RBersier/TPI_Horloge-Led-Capteurs/Image/Documentation/CDC/29156.jpg

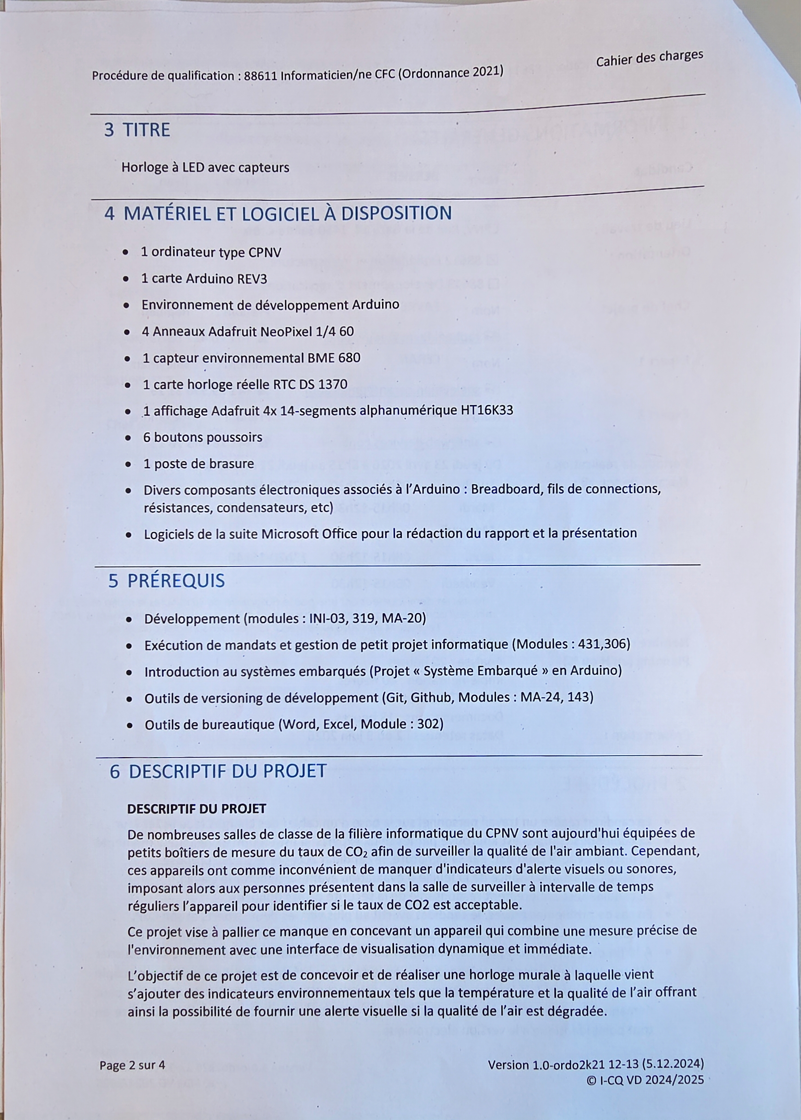
Image/Documentation/CDC/29156.jpg
