RBersier/TPI_Horloge-Led-Capteurs/Documentation/Video/Base/Red_circle_frame_transparent.svg.png

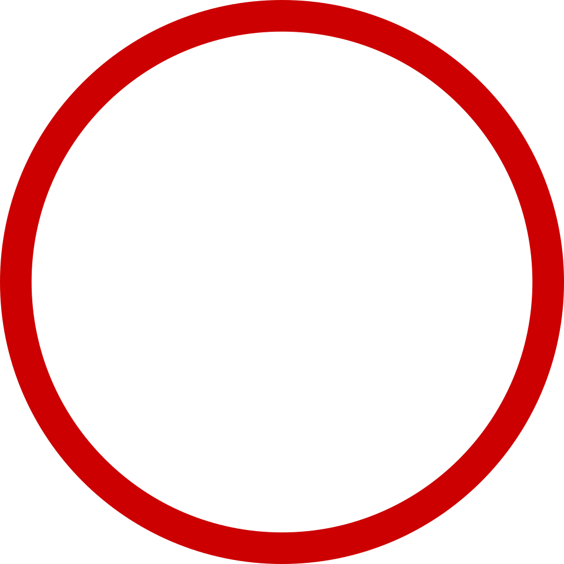
Documentation/Video/Base/Red_circle_frame_transparent.svg.png
