RBersier/TPI_Horloge-Led-Capteurs/Documentation/Video/Base/Rounded Arrow - Vertical.png

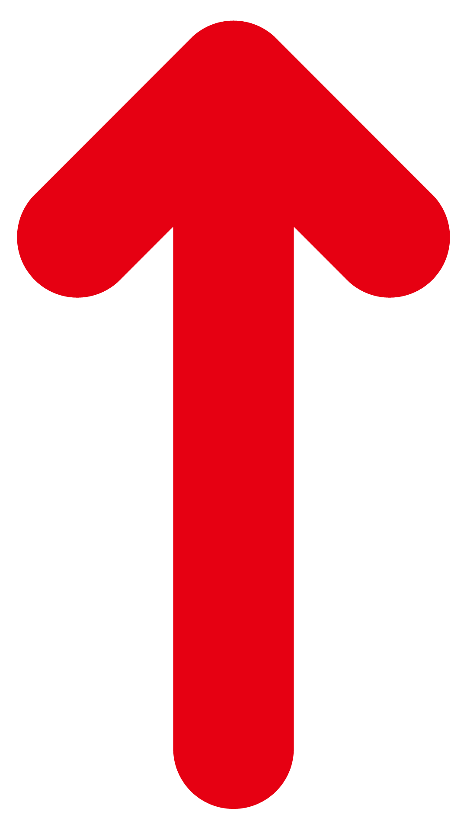
Documentation/Video/Base/Rounded Arrow - Vertical.png
