RBersier/TPI_Horloge-Led-Capteurs/Image/Documentation/CDC/29155.jpg

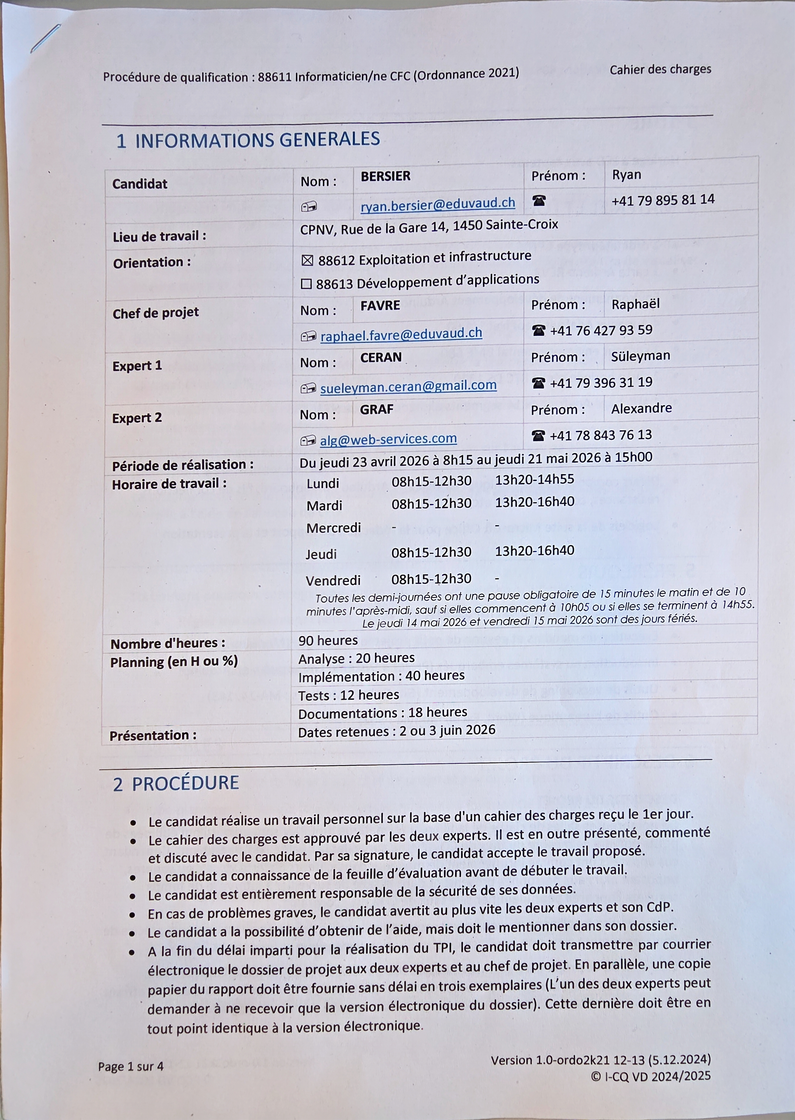
Image/Documentation/CDC/29155.jpg
