RBersier/TPI_Horloge-Led-Capteurs/Image/Documentation/CDC/29157.jpg

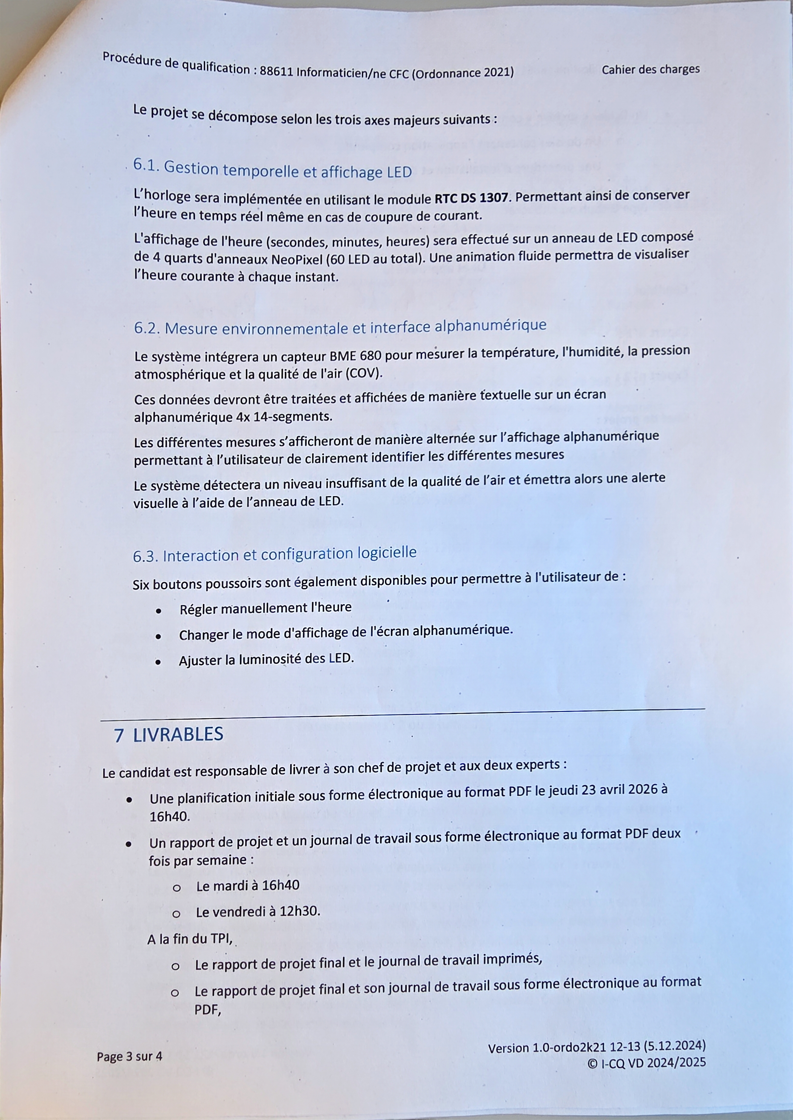
Image/Documentation/CDC/29157.jpg
