RBersier/TPI_Horloge-Led-Capteurs/Image/Documentation/CDC/29158.jpg

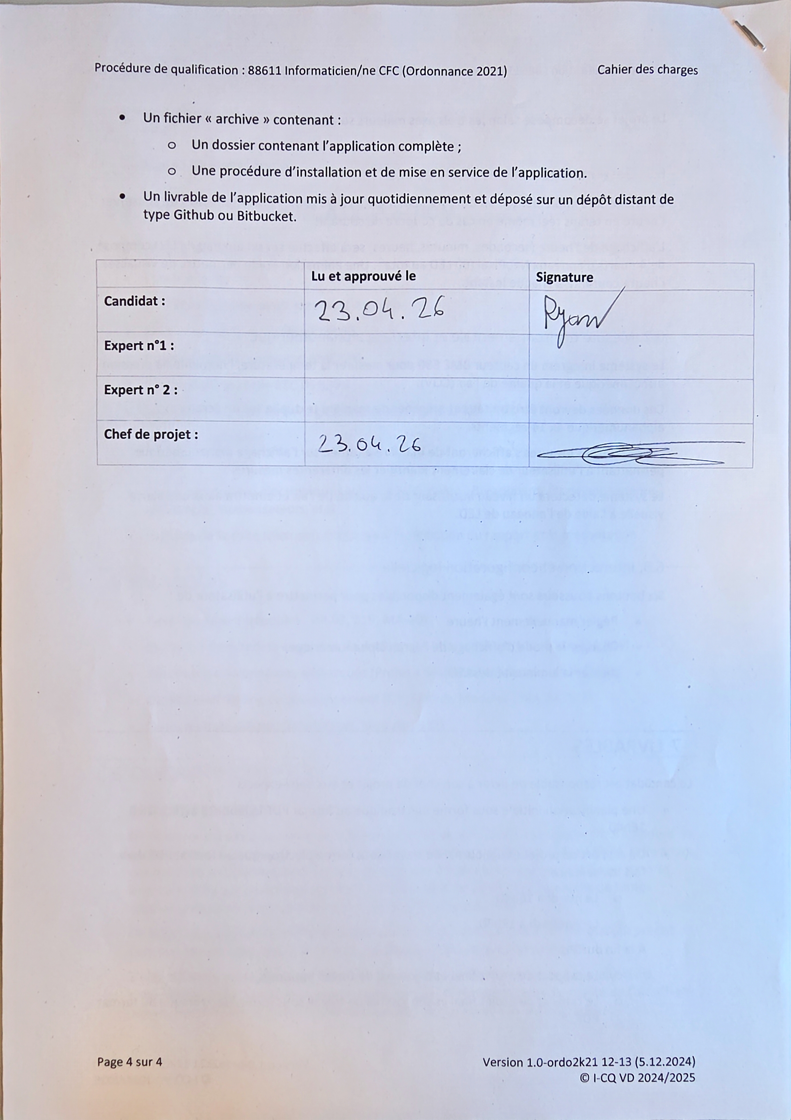
Image/Documentation/CDC/29158.jpg
