RBersier/TPI_Horloge-Led-Capteurs/Image/Documentation/Planning/final/Planification_TPI_Ryan-Bersier-final-images-5.jpg

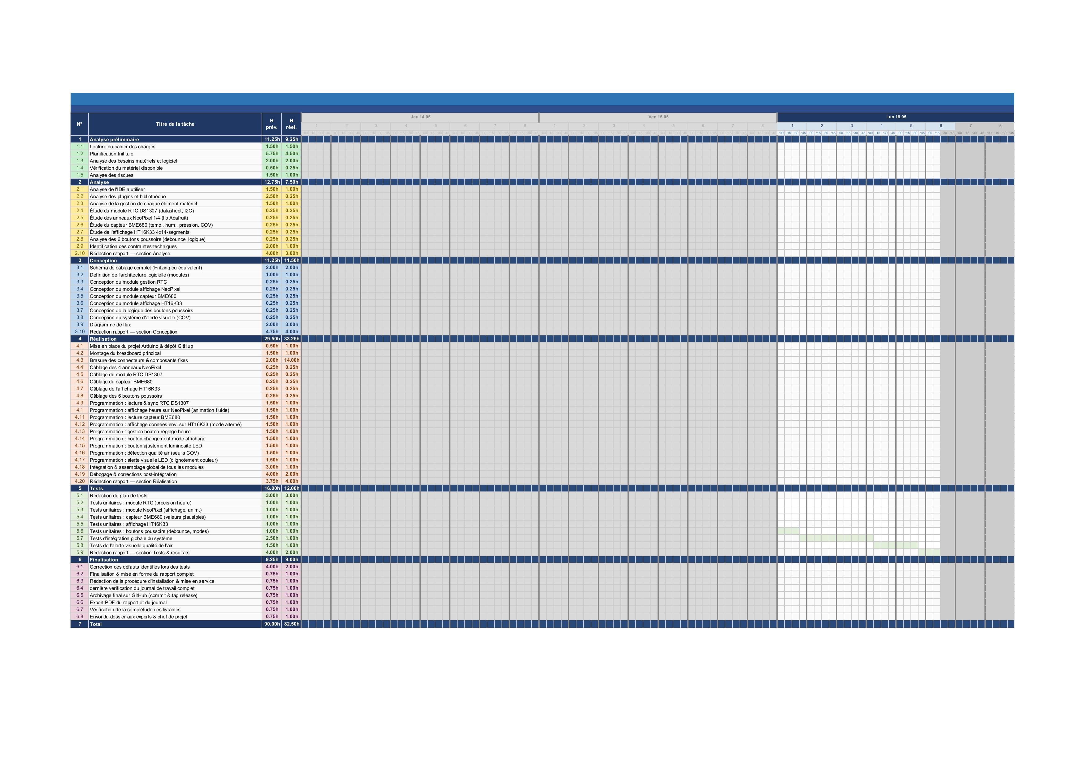
Image/Documentation/Planning/final/Planification_TPI_Ryan-Bersier-final-images-5.jpg
