RBersier/TPI_Horloge-Led-Capteurs/Image/Documentation/Planning/initial/Planification_TPI_Ryan-Bersier-vide-images-6.jpg

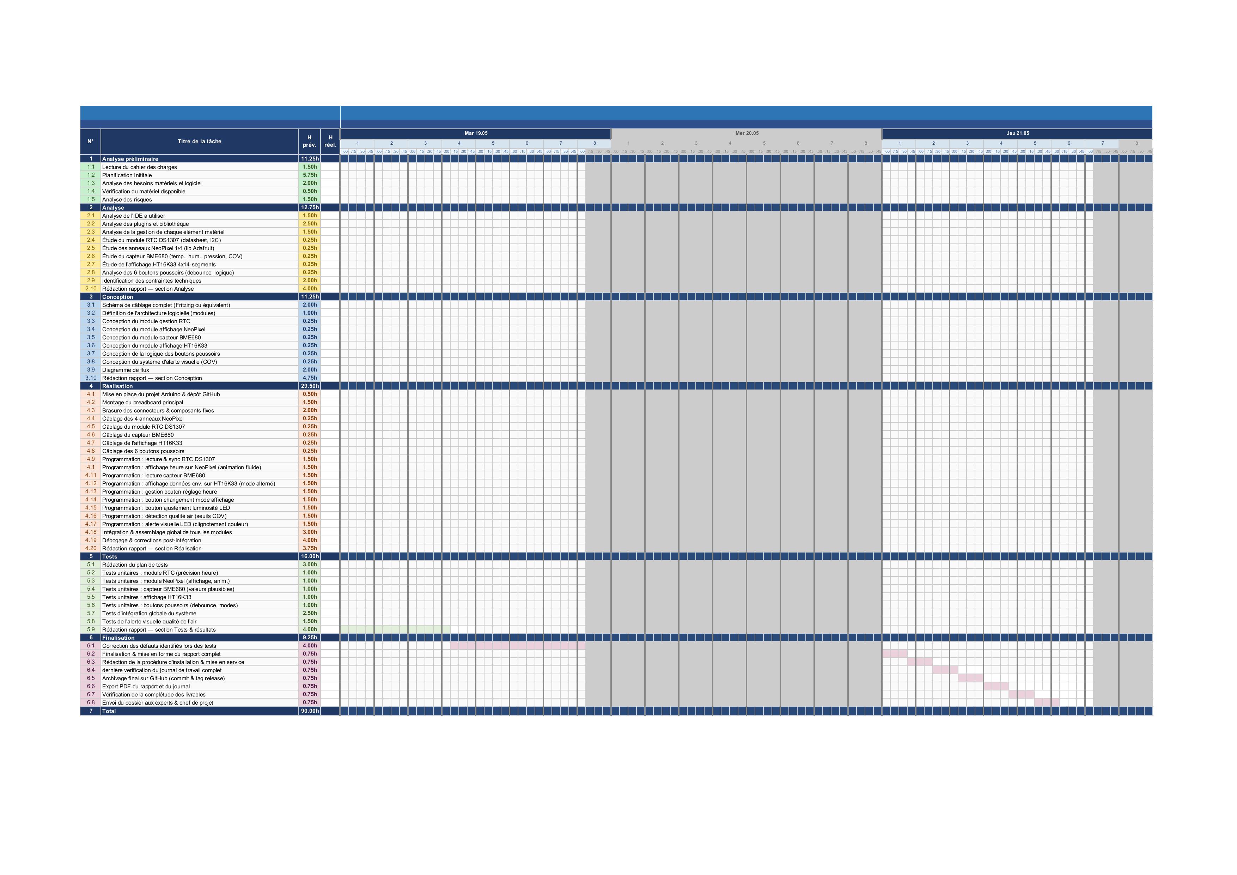
Image/Documentation/Planning/initial/Planification_TPI_Ryan-Bersier-vide-images-6.jpg
