RBersier/TPI_Horloge-Led-Capteurs/Image/Documentation/Schema/Diagramme-de-flux_TPI_Ryan-Bersier.drawio.png

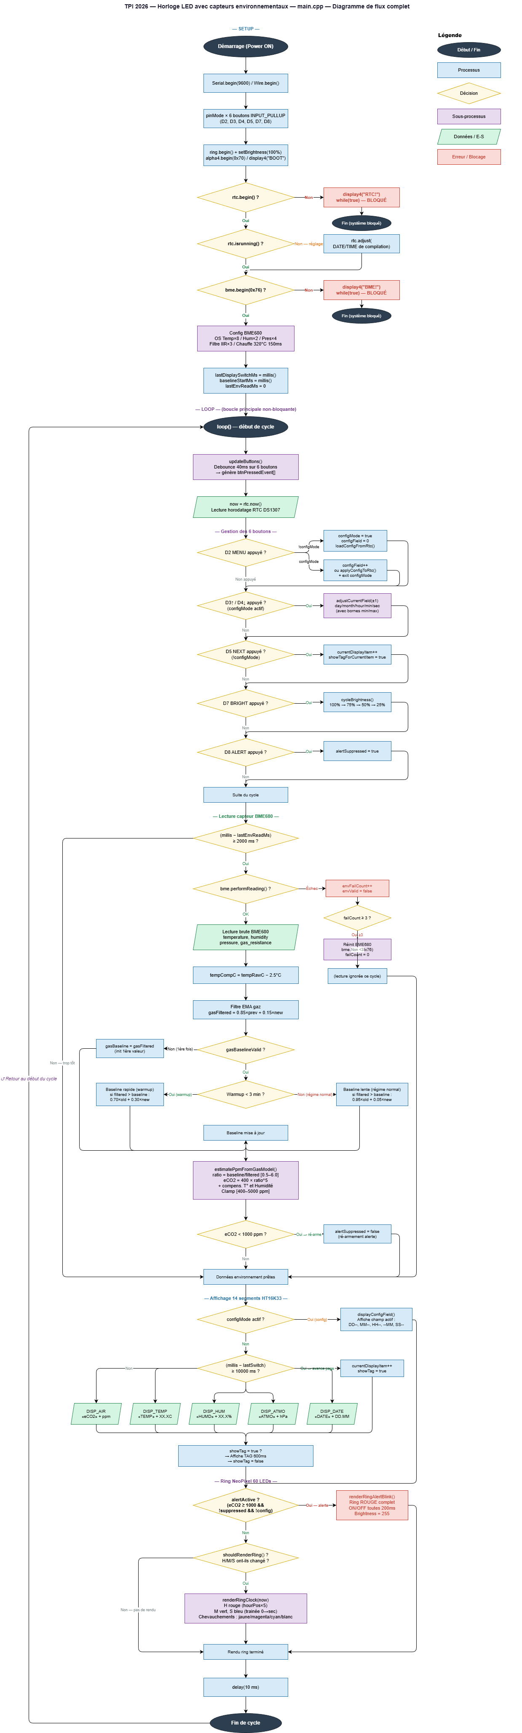
Image/Documentation/Schema/Diagramme-de-flux_TPI_Ryan-Bersier.drawio.png
