RBersier/TPI_Horloge-Led-Capteurs/Image/Materiel/1296_1756x2209.webp

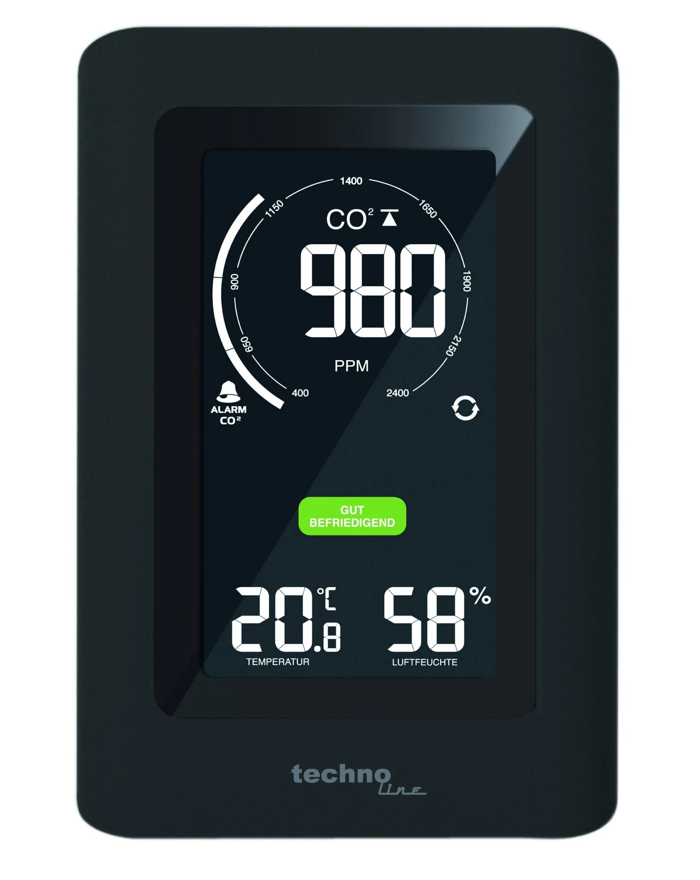
Image/Materiel/1296_1756x2209.webp
