RBersier/TPI_Horloge-Led-Capteurs/Image/Materiel/Média__6_-removebg-preview.png

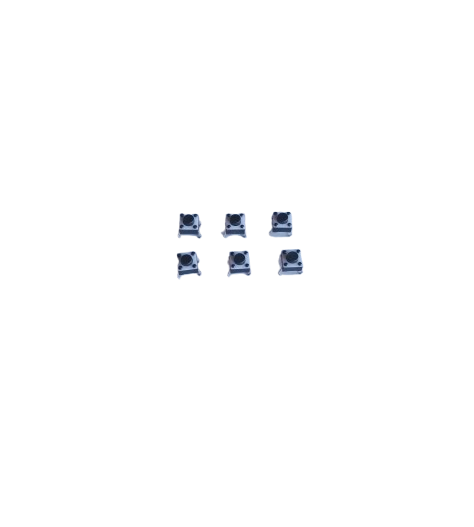
Image/Materiel/Média__6_-removebg-preview.png
