RBersier/TPI_Horloge-Led-Capteurs/Image/Materiel/PC.webp

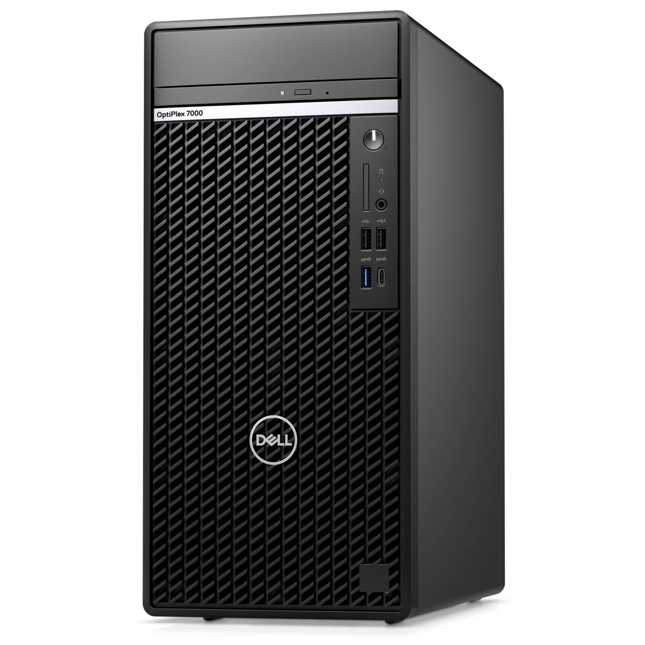
Image/Materiel/PC.webp
