RBersier/TPI_Horloge-Led-Capteurs/Image/Materiel/Untitled (1).png

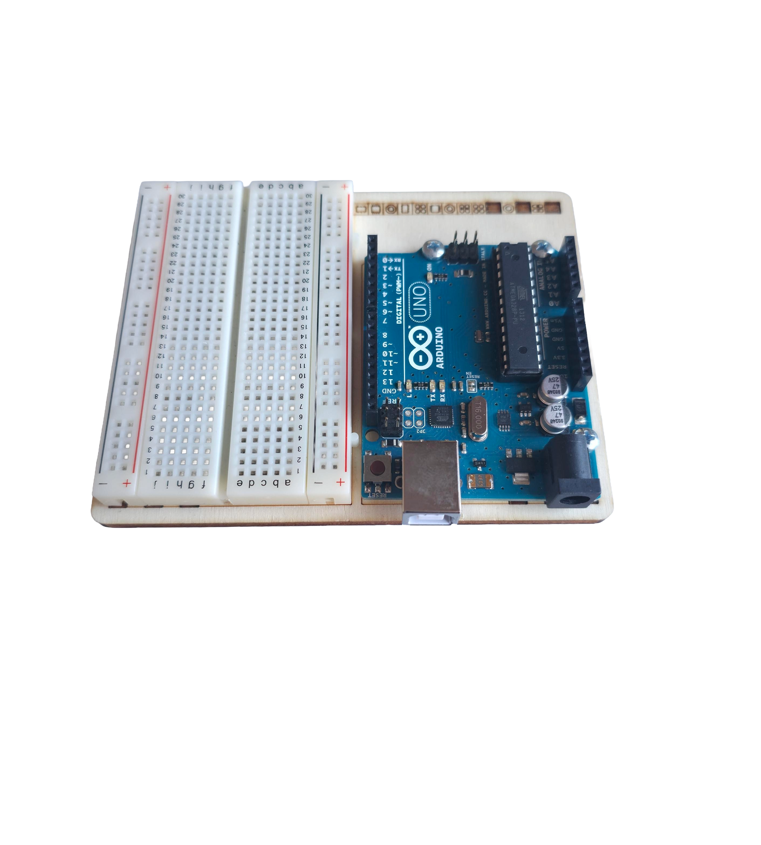
Image/Materiel/Untitled (1).png
