RBersier/TPI_Horloge-Led-Capteurs/Image/Materiel/Untitled (2).png

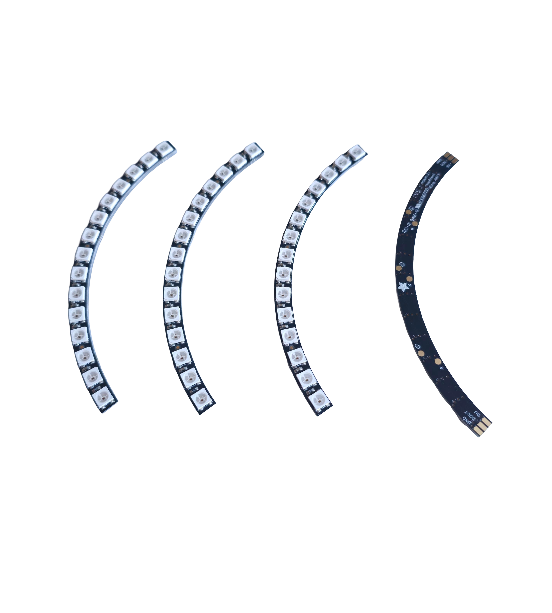
Image/Materiel/Untitled (2).png
