RBersier/TPI_Horloge-Led-Capteurs/Image/Materiel/Untitled (5).png

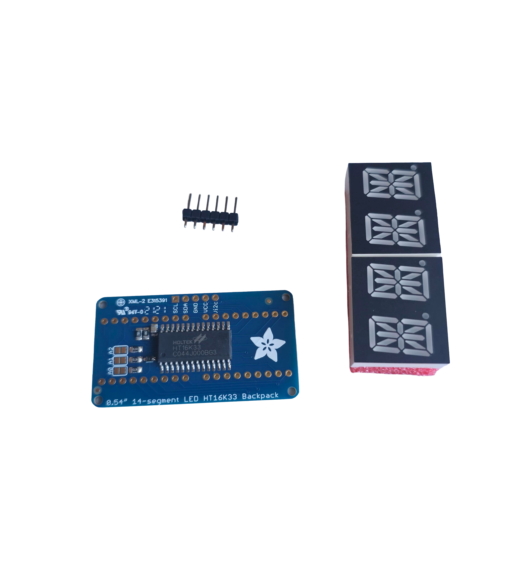
Image/Materiel/Untitled (5).png
