RBersier/TPI_Horloge-Led-Capteurs/Image/Materiel/Untitled (6).png

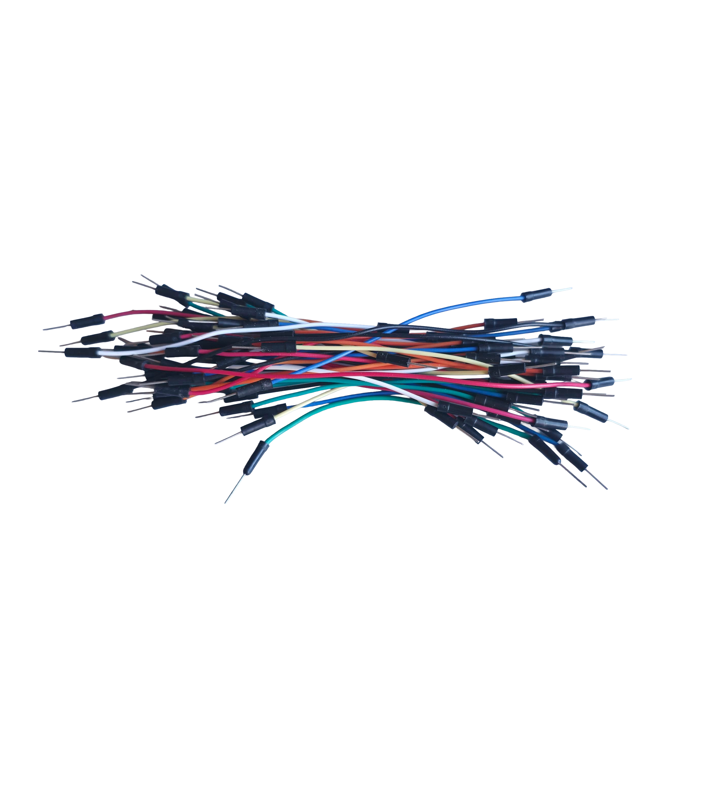
Image/Materiel/Untitled (6).png
