RBersier/TPI_Horloge-Led-Capteurs/Image/Materiel/Untitled (7).png

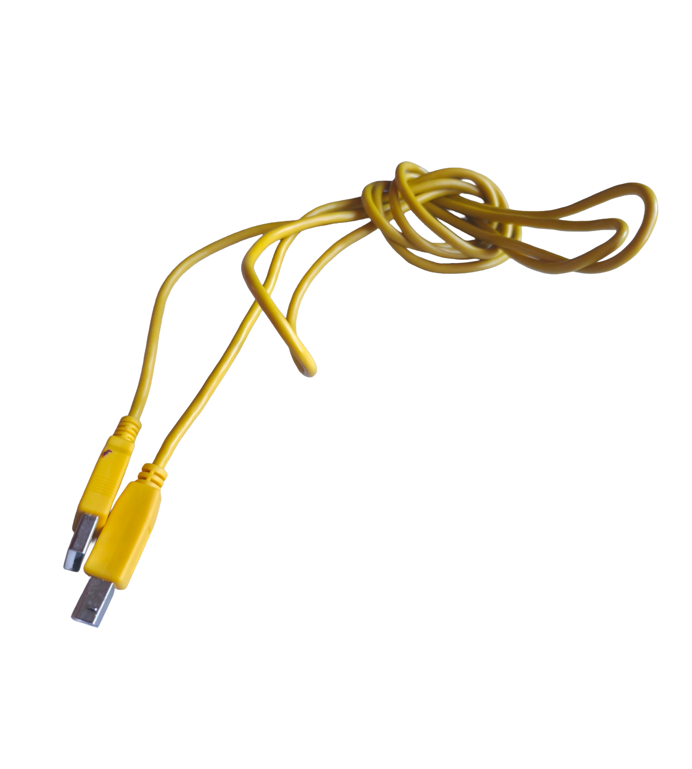
Image/Materiel/Untitled (7).png
