RBersier/TPI_Horloge-Led-Capteurs/Image/Documentation/Journal_De_Travail/Journal-de-Travail_TPI_Ryan-Bersier-images-0.jpg

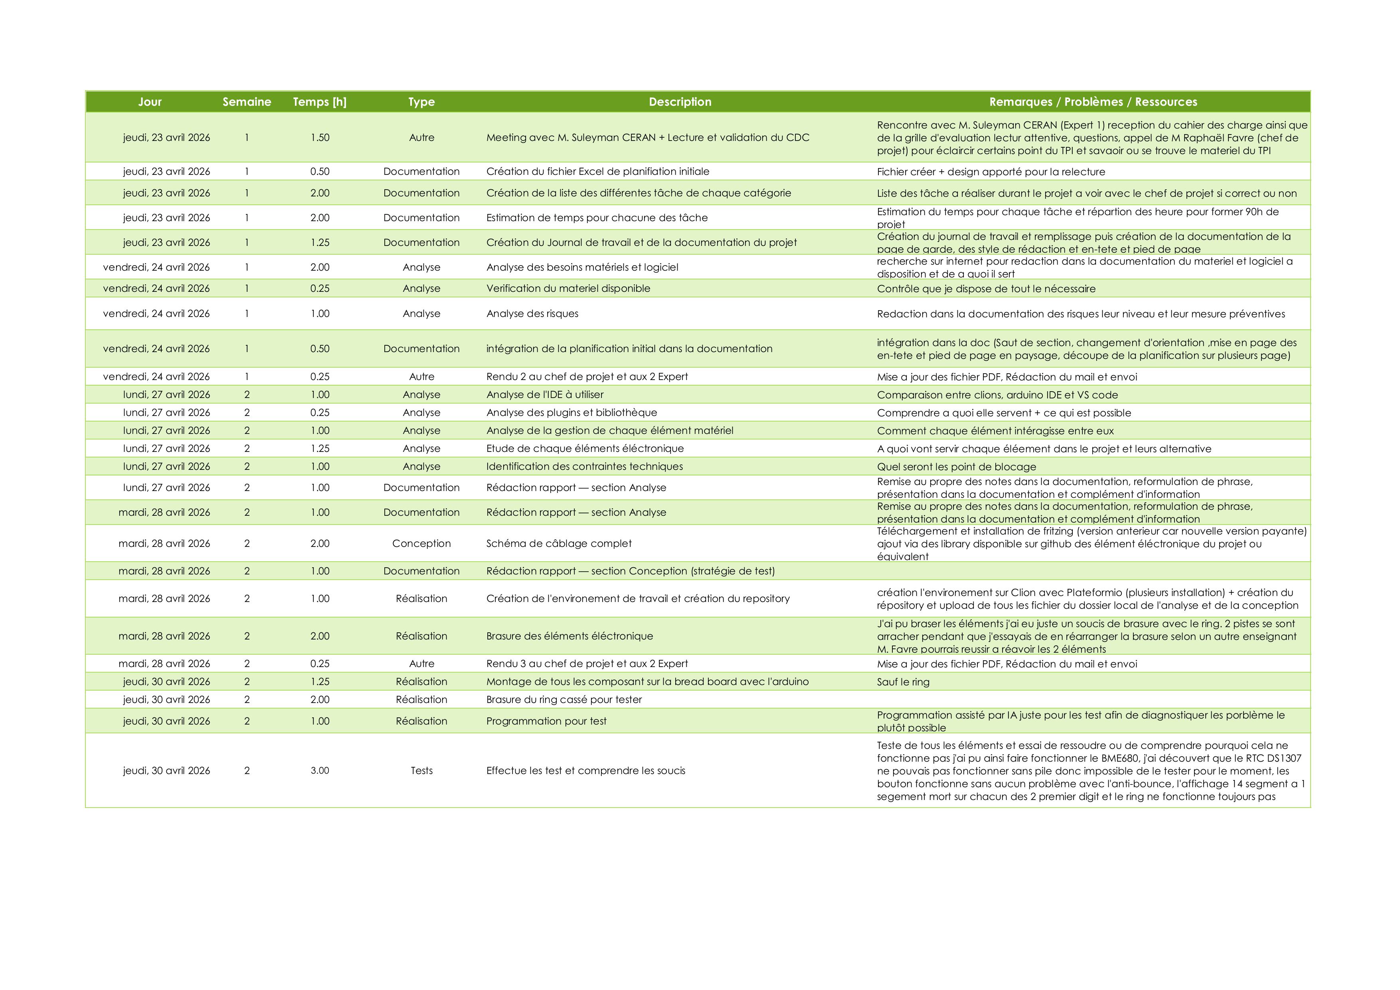
Image/Documentation/Journal_De_Travail/Journal-de-Travail_TPI_Ryan-Bersier-images-0.jpg
