RBersier/TPI_Horloge-Led-Capteurs/Image/Documentation/Journal_De_Travail/Journal-de-Travail_TPI_Ryan-Bersier-images-2.jpg

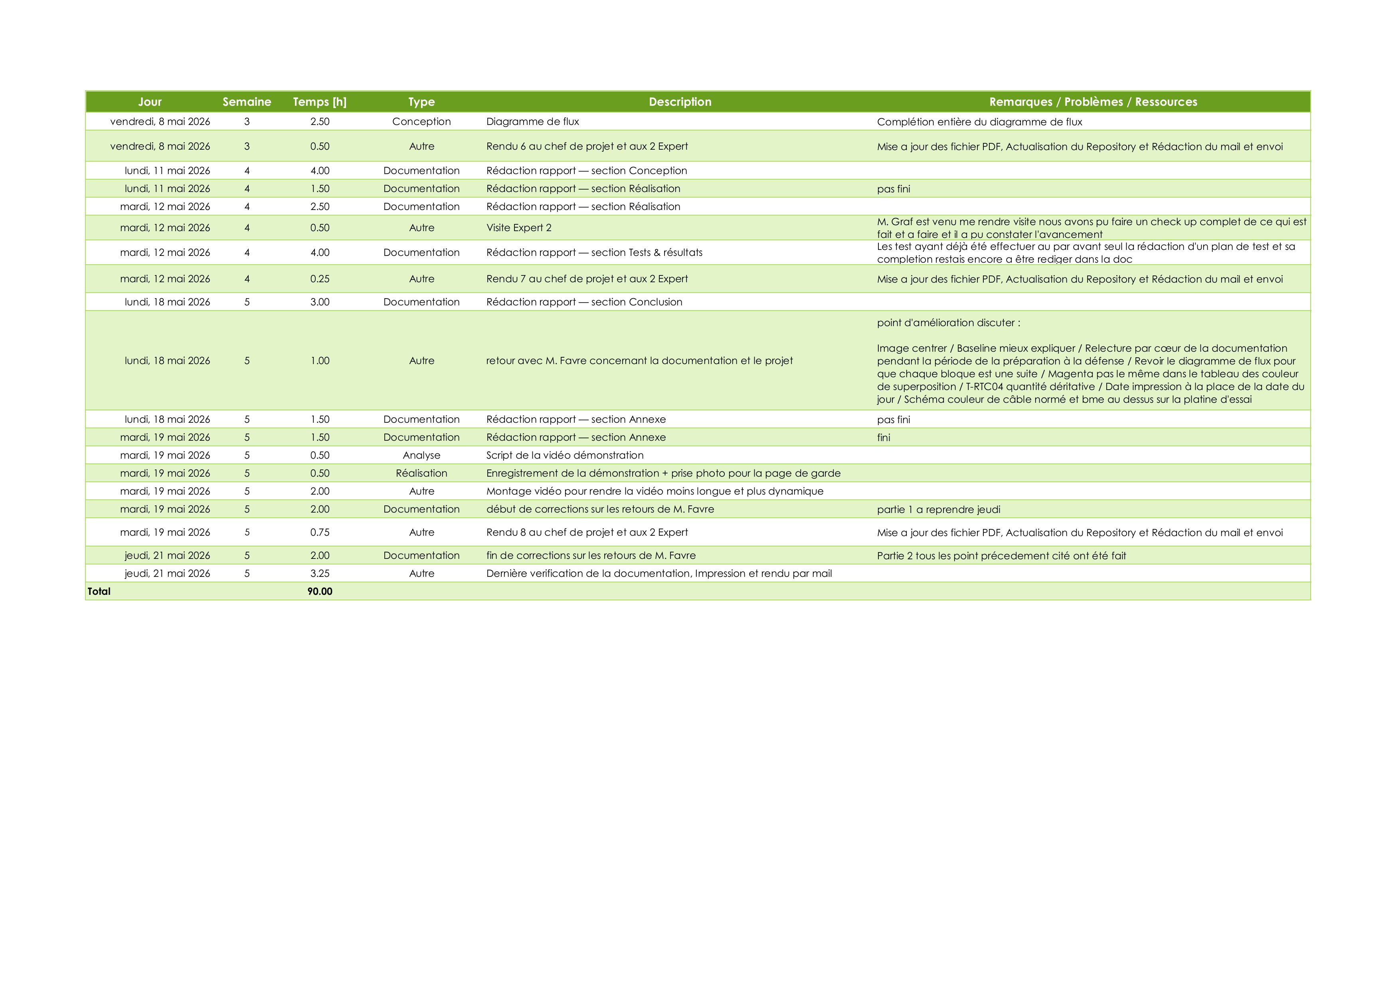
Image/Documentation/Journal_De_Travail/Journal-de-Travail_TPI_Ryan-Bersier-images-2.jpg
